camren-m/GeigerSat2/cad/Exports/Misc/Breadboard Mounting Plate.stl

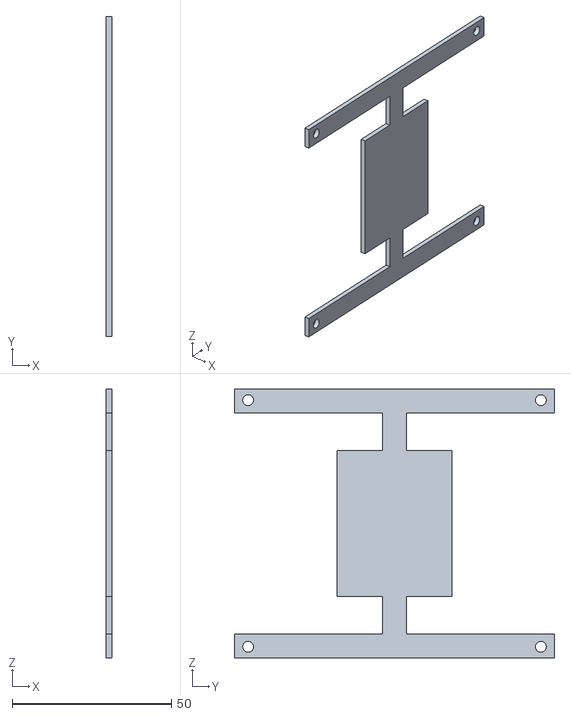
[picture p16: CAD file, 2023-04-28]
cad/Exports/Misc/Breadboard Mounting Plate.stl
1.75 x 100.5 x 84.5
