camren-m/GeigerSat2/cad/Exports/Misc/Geiger Cover/Molds/Side/Geiger Cover Side Mold Cover.stl

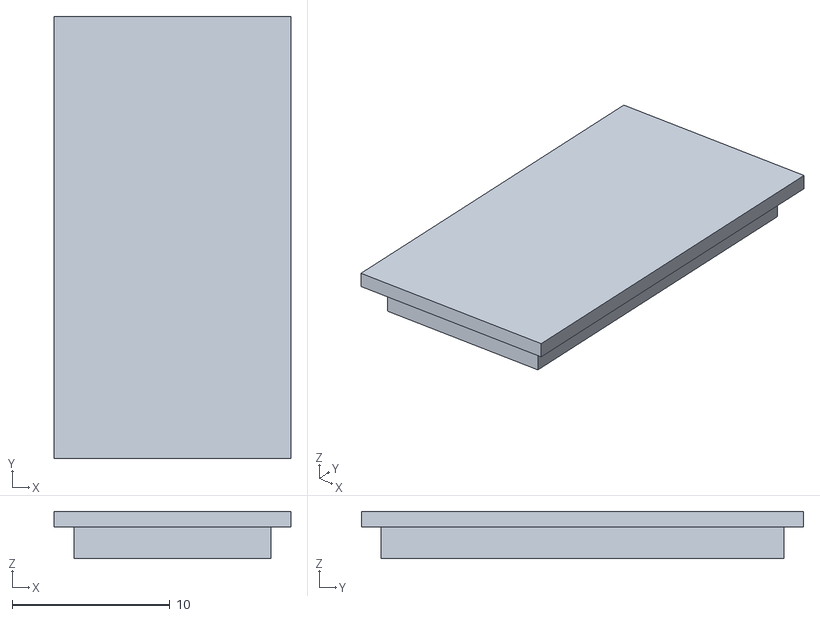
[picture p17: CAD file, 2023-04-28]
cad/Exports/Misc/Geiger Cover/Molds/Side/Geiger Cover Side Mold Cover.stl
15.0 x 28.0 x 3.00
